InputBlackBoxOutput/INGAME/documents/reference circuits/AO3401A - Charge switch.png

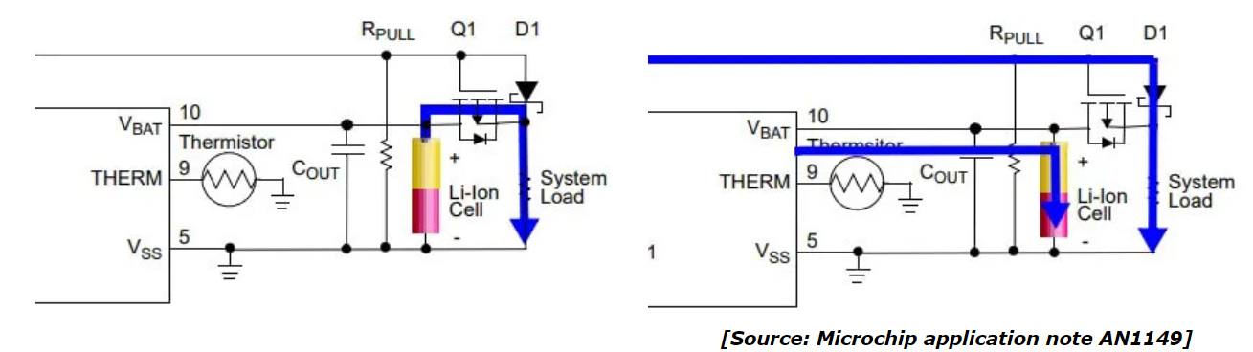
documents/reference circuits/AO3401A - Charge switch.png
