InputBlackBoxOutput/INGAME/documents/reference circuits/MPU6050 - Gyroscope and Accelerometer.png

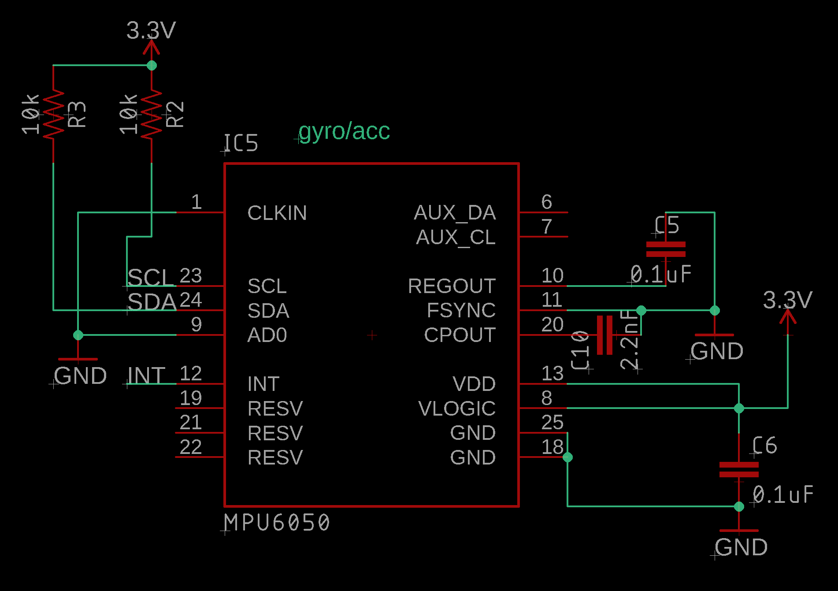
documents/reference circuits/MPU6050 - Gyroscope and Accelerometer.png
