InputBlackBoxOutput/INGAME/modules/Controller module/enclosure/3D-model-files/blue.PNG

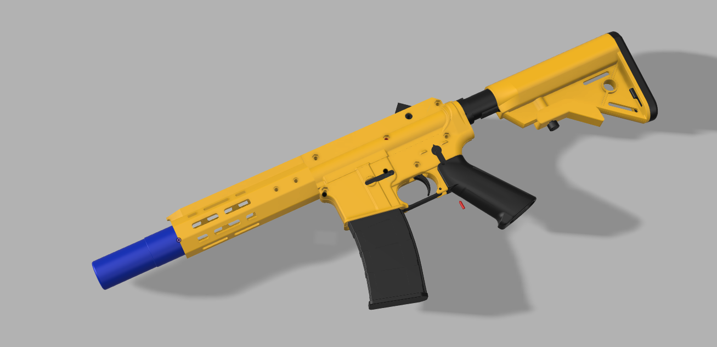
modules/Controller module/enclosure/3D-model-files/blue.PNG
