InputBlackBoxOutput/INGAME/modules/Controller module/enclosure/3D-model-files/red.PNG

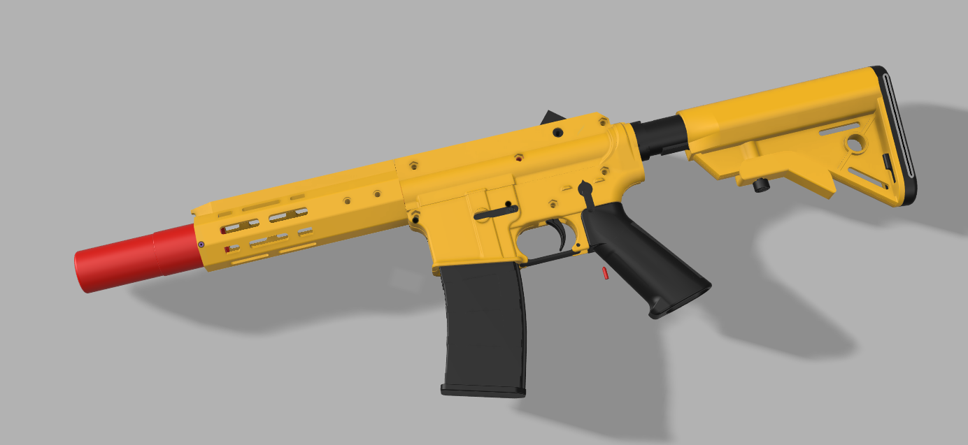
modules/Controller module/enclosure/3D-model-files/red.PNG
