InputBlackBoxOutput/INGAME/modules/Controller module/enclosure/3D-model-files/Handguard_plug.stl

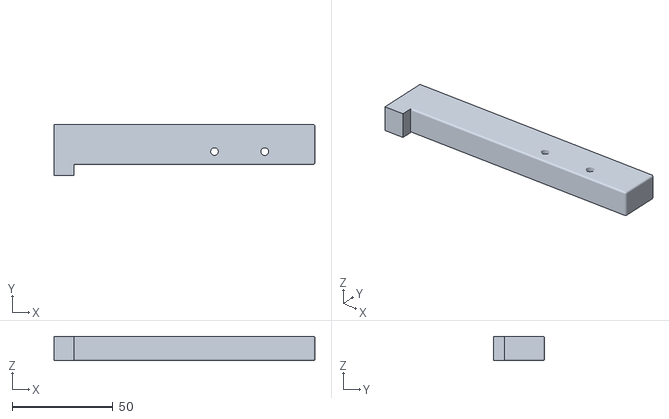
[picture p23: CAD file, 2023-04-24]
modules/Controller module/enclosure/3D-model-files/Handguard_plug.stl
129.8 x 25.5 x 12.0
