InputBlackBoxOutput/INGAME/modules/Controller module/enclosure/3D-model-files/Magcatch_button.stl

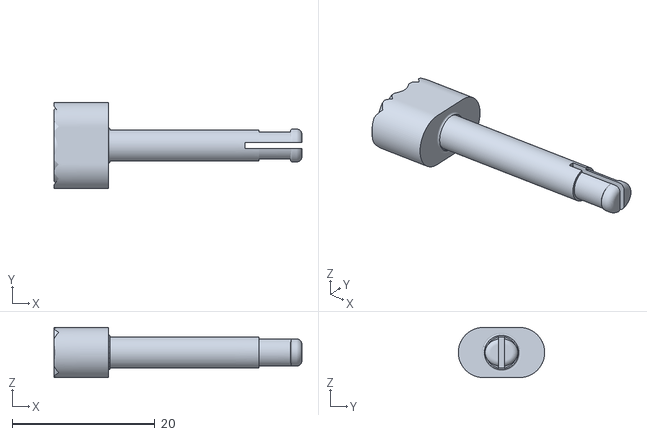
[picture p24: CAD file, 2023-04-24]
modules/Controller module/enclosure/3D-model-files/Magcatch_button.stl
34.7 x 12.1 x 7.00
