InputBlackBoxOutput/INGAME/modules/Controller module/enclosure/3D-model-files/End_plate.stl

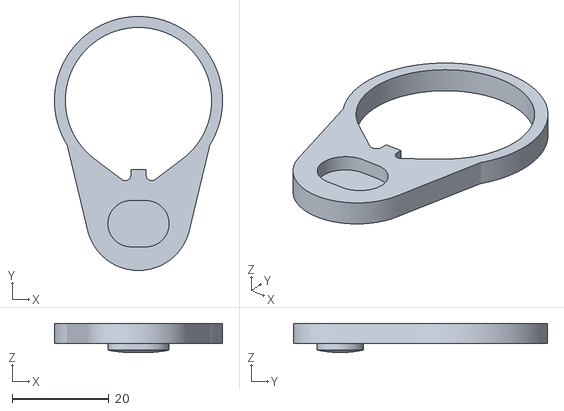
[picture p25: CAD file, 2023-04-24]
modules/Controller module/enclosure/3D-model-files/End_plate.stl
34.7 x 52.4 x 6.00
