InputBlackBoxOutput/INGAME/modules/Controller module/enclosure/3D-model-files/Trigger_guard.stl

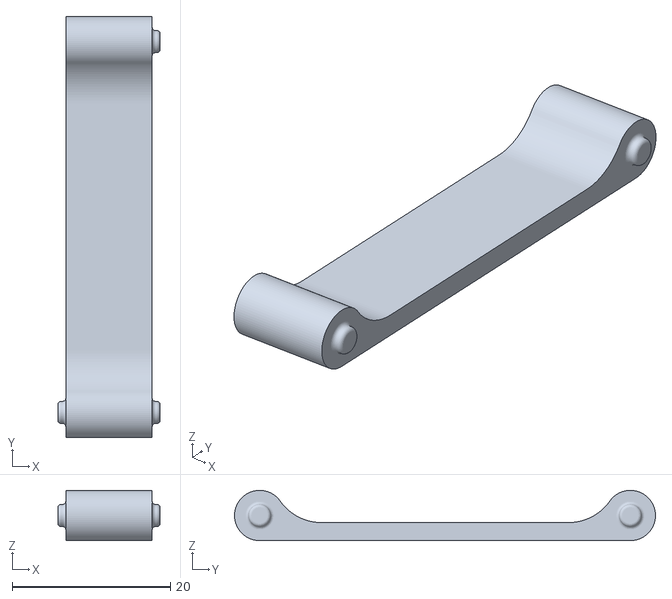
[picture p26: CAD file, 2023-04-24]
modules/Controller module/enclosure/3D-model-files/Trigger_guard.stl
12.9 x 53.2 x 6.35
