InputBlackBoxOutput/INGAME/modules/Controller module/enclosure/3D-model-files/Handguard.stl

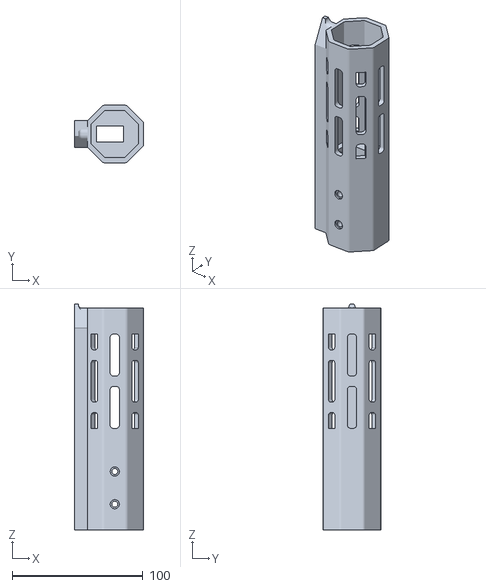
[picture p27: CAD file, 2023-04-24]
modules/Controller module/enclosure/3D-model-files/Handguard.stl
52.8 x 44.0 x 172.7
