InputBlackBoxOutput/INGAME/modules/Controller module/enclosure/3D-model-files/Stock_pin.stl

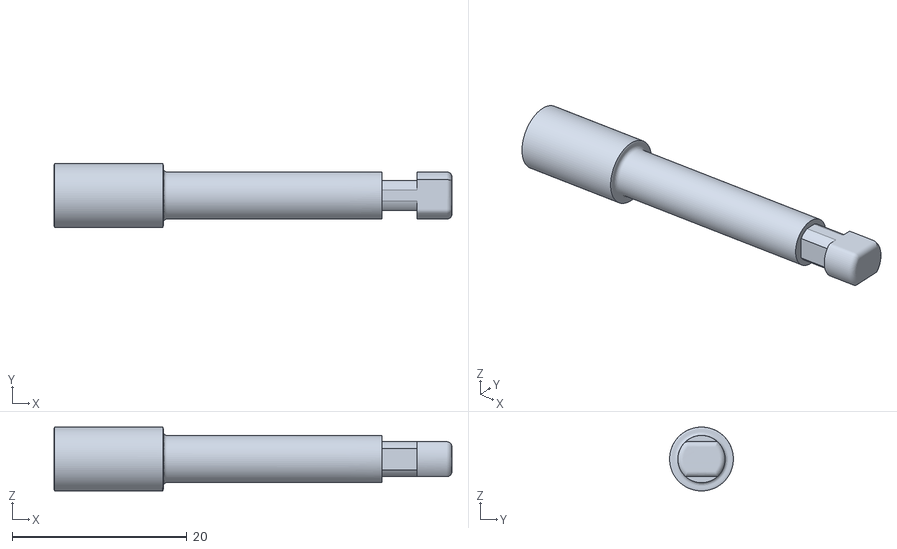
[picture p28: CAD file, 2023-04-24]
modules/Controller module/enclosure/3D-model-files/Stock_pin.stl
45.5 x 7.30 x 7.31
