InputBlackBoxOutput/INGAME/modules/Controller module/firmware/src/connections.h

// PIN CONNECTIONS

#define B31_PIN 13 // TRIGGER
#define B32_PIN 5  // STOCK
#define B33_PIN 12 // MAGZINE

#define B11_PIN 35
#define B12_PIN 34
#define B13_PIN 33
#define B14_PIN 32

#define B21_PIN 17
#define B22_PIN 16
#define B23_PIN 23

#define LEDR_PIN 25
#define LEDG_PIN 26
#define LEDB_PIN 27

#define LAZER_PIN  14
#define BUZZER_PIN 15

#define BATT_ADC_PIN 4
