InputBlackBoxOutput/INGAME/modules/Controller module/firmware/src/IMU-Fusion.cpp

#include "IMU-Fusion.h"

Fusion::Fusion()
{
    FusionOffsetInitialise(&offset, SAMPLE_RATE);
    FusionAhrsInitialise(&ahrs);

    // Set AHRS algorithm settings
    const FusionAhrsSettings settings = {
        .gain = 0.5f,
        .accelerationRejection = 10.0f,
        .magneticRejection = 20.0f,
        .rejectionTimeout = 5 * SAMPLE_RATE, /* 5 seconds */
    };
    FusionAhrsSetSettings(&ahrs, &settings);

    // Replace with actual calibration data
    gyroscopeMisalignment = {1.0f, 0.0f, 0.0f, 0.0f, 1.0f, 0.0f, 0.0f, 0.0f, 1.0f};
    gyroscopeSensitivity = {1.0f, 1.0f, 1.0f};
    gyroscopeOffset = {0.0f, 0.0f, 0.0f};
    accelerometerMisalignment = {1.0f, 0.0f, 0.0f, 0.0f, 1.0f, 0.0f, 0.0f, 0.0f, 1.0f};
    accelerometerSensitivity = {1.0f, 1.0f, 1.0f};
    accelerometerOffset = {0.0f, 0.0f, 0.0f};
    softIronMatrix = {1.0f, 0.0f, 0.0f, 0.0f, 1.0f, 0.0f, 0.0f, 0.0f, 1.0f};
    hardIronOffset = {0.0f, 0.0f, 0.0f};

}

// Call this function each time new gyroscope data is available
void Fusion::updateOrientation(FusionVector gyroscope, FusionVector accelerometer, FusionVector magnetometer, clock_t timestamp)
{
    // Apply calibration
    gyroscope = FusionCalibrationInertial(gyroscope, gyroscopeMisalignment, gyroscopeSensitivity, gyroscopeOffset);
    accelerometer = FusionCalibrationInertial(accelerometer, accelerometerMisalignment, accelerometerSensitivity, accelerometerOffset);
    magnetometer = FusionCalibrationMagnetic(magnetometer, softIronMatrix, hardIronOffset);

    // Update gyroscope offset correction algorithm
    gyroscope = FusionOffsetUpdate(&offset, gyroscope);

    // Calculate delta time (in seconds) to account for gyroscope sample clock error
    static clock_t previousTimestamp;
    const float deltaTime = (float)(timestamp - previousTimestamp) / (float)CLOCKS_PER_SEC;
    previousTimestamp = timestamp;

    // Update gyroscope AHRS algorithm
    FusionAhrsUpdate(&ahrs, gyroscope, accelerometer, magnetometer, deltaTime);

    const FusionEuler euler = FusionQuaternionToEuler(FusionAhrsGetQuaternion(&ahrs));

    roll = euler.angle.roll;
    pitch = euler.angle.pitch;
    yaw = euler.angle.yaw;
}
