InputBlackBoxOutput/INGAME/modules/Controller module/firmware/src/character-map.h

// CHARACTER MAP
#define JUMP_CHAR 'J'
#define WALK_CHAR 'W'
#define EXTRA_1_CHAR 'A'

#define CROUCH_CHAR 'C'
#define SPRINT_CHAR 'S'
#define EXTRA_2_CHAR 'B'

#define GRENADE_CHAR 'G'
#define PREVIOUS_WEAPON_CHAR 'P'
#define EXTRA_3_CHAR 'X'

#define KNIFE_CHAR 'K'
#define NEXT_WEAPON_CHAR 'N'
#define EXTRA_4_CHAR 'Y'

#define FIRE_CHAR 'F'
#define SCOPE_CHAR 'O'
#define RELOAD_CHAR 'R'
