InputBlackBoxOutput/INGAME/modules/HID module/firmware - ATmega32U4/src/key-map.h

// Mapping of game specific keyboard buttons to generic communication tokens

#define ACTION_FIRE MOUSE_LEFT
#define ACTION_SCOPE MOUSE_RIGHT
#define ACTION_RELOAD 'R'

#define ACTION_ESC KEY_ESC

#define ACTION_JUMP 'J'
#define ACTION_WALK 'W'
#define ACTION_EXTRA1 'A'

#define ACTION_CROUCH 'C'
#define ACTION_SPRINT 'S'
#define ACTION_EXTRA2 'B'

#define ACTION_GRENADE 'G'
#define ACTION_PREV_WEAPON 'P'
#define ACTION_EXTRA3 'X'

#define ACTION_KNIFE 'K'
#define ACTION_NEXT_WEAPON 'N'
#define ACTION_EXTRA4 'Y'
